jacobsa/dbnz/programmable_memory/schematics/Common control.png

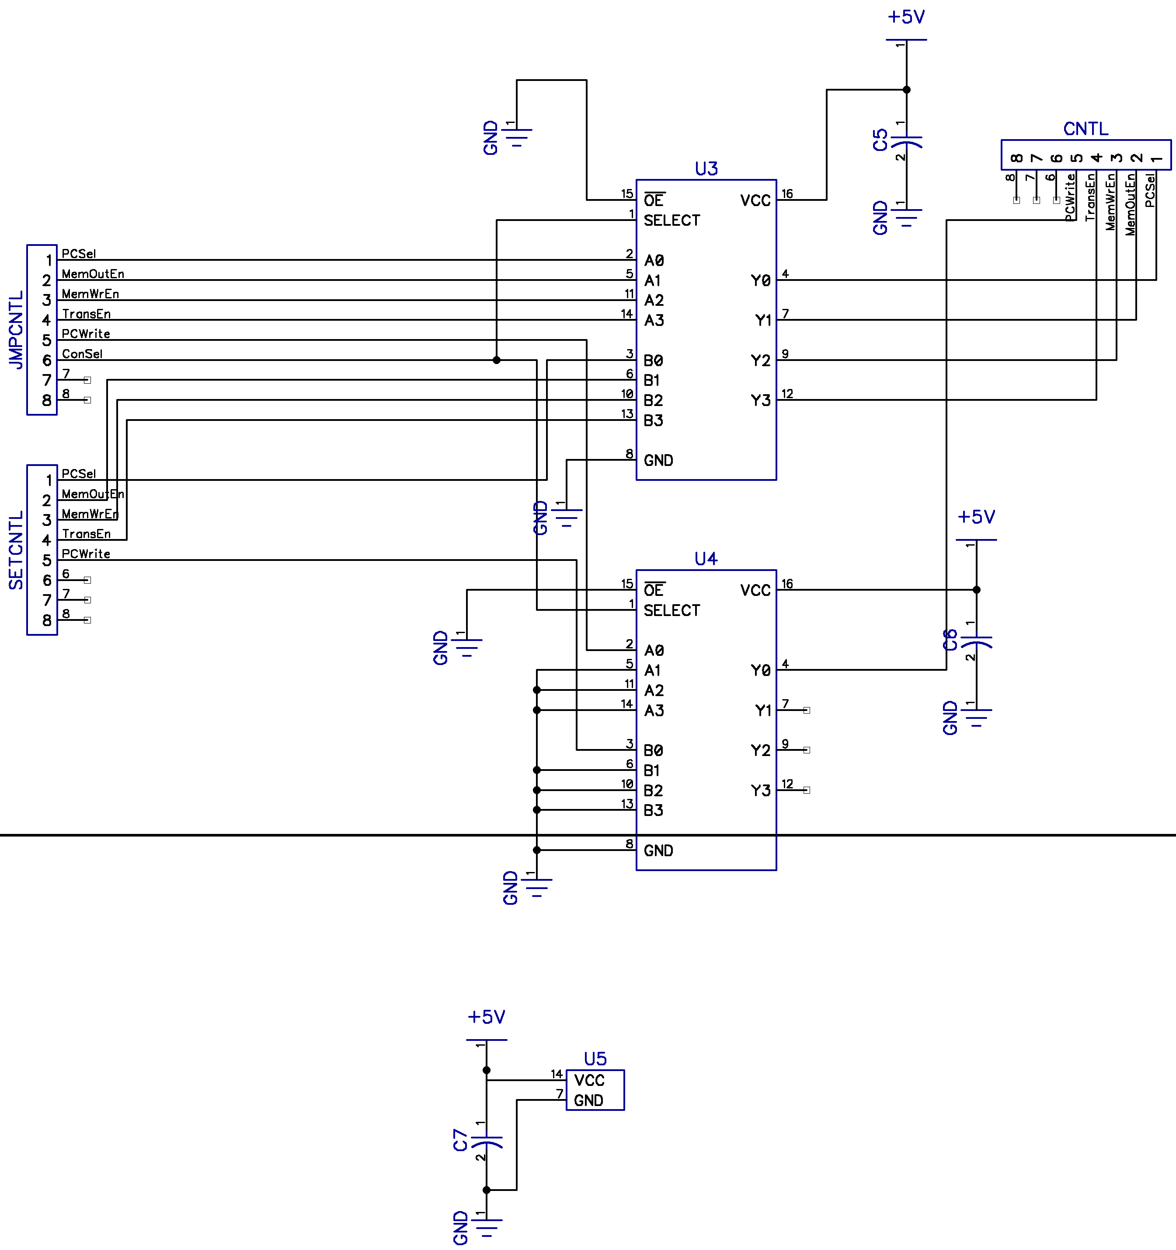
programmable_memory/schematics/Common control.png
