jacobsa/dbnz/programmable_memory/sketches/block_diagram.jpg

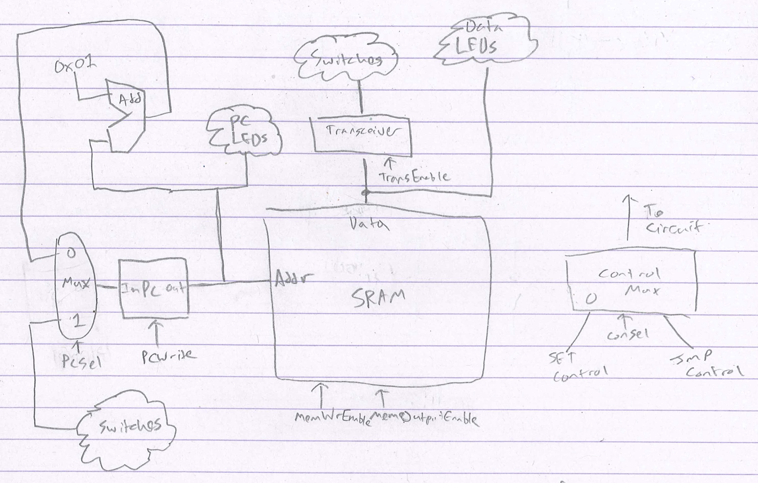
programmable_memory/sketches/block_diagram.jpg
