jacobsa/dbnz/programmable_memory/sketches/control_logic.jpg

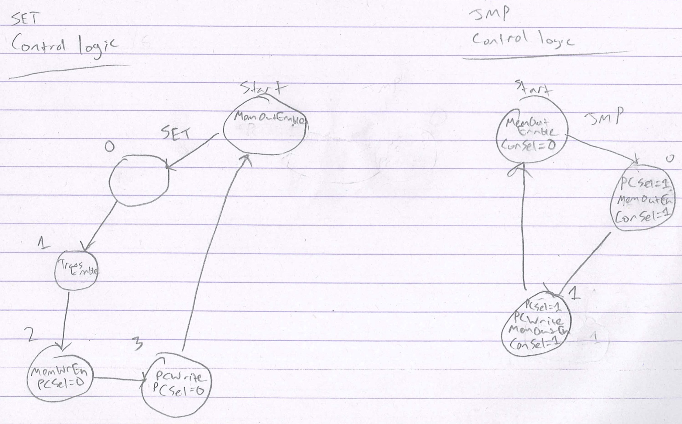
programmable_memory/sketches/control_logic.jpg
